vik-bak/LUMEN-2025_BUIFER/LUMEN_STM_Micro/Core/Inc/usr_general.h

#ifndef USR_GENERAL_H_
#define USR_GENERAL_H_

#define bool _Bool
#define _io static

#define true 1
#define false 0

#include <stdio.h>
#include <stdlib.h>
#include <math.h>
#include <string.h>
#include <stdbool.h>
#include "stm32l4xx_hal.h"
#include "usr_gnss_parser.h"

#endif
